Cespresso/CLumo/standalone/src/assets.rs

#![allow(dead_code)]

/// 8x8 LED matrix dot patterns.
/// Each `[u8; 8]` represents 8 rows, MSB=left pixel, LSB=right pixel.

// --- Faces ---

pub const FACE_SMILE: [u8; 8] = [0x00, 0x66, 0x66, 0x00, 0x00, 0x42, 0x3C, 0x00];
pub const FACE_BLINK: [u8; 8] = [0x00, 0x00, 0x66, 0x00, 0x00, 0x42, 0x3C, 0x00];
pub const FACE_SAD: [u8; 8] = [0x00, 0x66, 0x66, 0x00, 0x00, 0x3C, 0x42, 0x00];
pub const FACE_ANGRY: [u8; 8] = [0x00, 0x42, 0x66, 0x00, 0x00, 0x3C, 0x42, 0x00];
pub const FACE_HAPPY: [u8; 8] = [0x00, 0x66, 0x66, 0x00, 0x24, 0x42, 0x3C, 0x00];
pub const FACE_LOOK_LEFT: [u8; 8] = [0x00, 0xCC, 0xCC, 0x00, 0x00, 0x42, 0x3C, 0x00];
pub const FACE_LOOK_RIGHT: [u8; 8] = [0x00, 0x33, 0x33, 0x00, 0x00, 0x42, 0x3C, 0x00];

// --- Mode icons ---

pub const ICON_PET: [u8; 8] = FACE_SMILE;
/// An hourglass.
pub const ICON_POMODORO: [u8; 8] = [0x7E, 0x42, 0x24, 0x18, 0x18, 0x24, 0x42, 0x7E];
pub const ICON_DICE: [u8; 8] = DICE_5;

// --- Dice (1-6) ---

pub const DICE_1: [u8; 8] = [0x00, 0x00, 0x00, 0x18, 0x18, 0x00, 0x00, 0x00];
pub const DICE_2: [u8; 8] = [0x00, 0x60, 0x60, 0x00, 0x00, 0x06, 0x06, 0x00];
pub const DICE_3: [u8; 8] = [0x00, 0x60, 0x60, 0x18, 0x18, 0x06, 0x06, 0x00];
pub const DICE_4: [u8; 8] = [0x00, 0x66, 0x66, 0x00, 0x00, 0x66, 0x66, 0x00];
pub const DICE_5: [u8; 8] = [0x00, 0x66, 0x66, 0x18, 0x18, 0x66, 0x66, 0x00];
pub const DICE_6: [u8; 8] = [0x00, 0x66, 0x66, 0x66, 0x66, 0x66, 0x66, 0x00];

// --- Utility ---

pub const PATTERN_ALL_ON: [u8; 8] = [0xFF; 8];
pub const PATTERN_ALL_OFF: [u8; 8] = [0x00; 8];
