Cespresso/CLumo/companion/android/app/src/main/java/io/github/cespresso/clumo/ui/components/Components.kt

package io.github.cespresso.clumo.ui.components

import androidx.compose.animation.animateColor
import androidx.compose.animation.core.RepeatMode
import androidx.compose.animation.core.animateFloat
import androidx.compose.animation.core.infiniteRepeatable
import androidx.compose.animation.core.rememberInfiniteTransition
import androidx.compose.animation.core.tween
import androidx.compose.foundation.Canvas
import androidx.compose.foundation.background
import androidx.compose.foundation.border
import androidx.compose.foundation.clickable
import androidx.compose.foundation.interaction.MutableInteractionSource
import androidx.compose.foundation.layout.Arrangement
import androidx.compose.foundation.layout.Box
import androidx.compose.foundation.layout.Column
import androidx.compose.foundation.layout.ColumnScope
import androidx.compose.foundation.layout.Row
import androidx.compose.foundation.layout.fillMaxSize
import androidx.compose.foundation.layout.fillMaxWidth
import androidx.compose.foundation.layout.offset
import androidx.compose.foundation.layout.padding
import androidx.compose.foundation.layout.size
import androidx.compose.foundation.shape.CircleShape
import androidx.compose.foundation.shape.RoundedCornerShape
import androidx.compose.foundation.text.BasicTextField
import androidx.compose.material3.Slider
import androidx.compose.material3.SliderDefaults
import androidx.compose.material3.Text
import androidx.compose.runtime.Composable
import androidx.compose.runtime.getValue
import androidx.compose.runtime.mutableStateOf
import androidx.compose.runtime.remember
import androidx.compose.runtime.setValue
import androidx.compose.ui.Alignment
import androidx.compose.ui.Modifier
import androidx.compose.ui.draw.clip
import androidx.compose.ui.draw.drawBehind
import androidx.compose.ui.draw.shadow
import androidx.compose.ui.geometry.CornerRadius
import androidx.compose.ui.geometry.Offset
import androidx.compose.ui.geometry.Rect
import androidx.compose.ui.geometry.RoundRect
import androidx.compose.ui.graphics.Brush
import androidx.compose.ui.graphics.Color
import androidx.compose.ui.graphics.Path
import androidx.compose.ui.graphics.PathEffect
import androidx.compose.ui.graphics.PathOperation
import androidx.compose.ui.graphics.StrokeCap
import androidx.compose.ui.graphics.StrokeJoin
import androidx.compose.ui.graphics.drawscope.Stroke
import androidx.compose.ui.graphics.lerp
import androidx.compose.ui.res.stringResource
import androidx.compose.ui.semantics.Role
import androidx.compose.ui.semantics.contentDescription
import androidx.compose.ui.semantics.semantics
import androidx.compose.ui.text.TextStyle
import androidx.compose.ui.text.font.FontWeight
import androidx.compose.ui.text.style.TextAlign
import androidx.compose.ui.unit.Dp
import androidx.compose.ui.unit.dp
import androidx.compose.ui.unit.sp
import androidx.compose.ui.zIndex
import io.github.cespresso.clumo.R
import io.github.cespresso.clumo.design.ClumoColors
import io.github.cespresso.clumo.design.ContentTone
import io.github.cespresso.clumo.design.contentToneFor
import io.github.cespresso.clumo.domain.ConnectionState
import io.github.cespresso.clumo.domain.DeviceAppearance
import io.github.cespresso.clumo.ui.theme.LocalClumoAccents
import io.github.cespresso.clumo.ui.theme.RoundedFontFamily

// ---------------------------------------------------------------------------
// Connection-state visuals
// ---------------------------------------------------------------------------

@Composable
fun connectionLabel(state: ConnectionState): Pair<String, Color> =
    when (state) {
        ConnectionState.Ready -> stringResource(R.string.state_connected) to LocalClumoAccents.current.accent
        ConnectionState.Connecting,
        ConnectionState.Reconnecting,
        ConnectionState.Bonding,
        ConnectionState.Connected,
        ConnectionState.Synchronizing,
        -> stringResource(R.string.state_connecting) to ClumoColors.Muted
        ConnectionState.Error -> stringResource(R.string.state_error) to ClumoColors.Coral
        ConnectionState.Disconnected -> stringResource(R.string.state_disconnected) to ClumoColors.MutedLight
    }

// ---------------------------------------------------------------------------
// Brand motif: thick rounded L-corner stroke
// ---------------------------------------------------------------------------

@Composable
fun BrandCorner(
    size: Dp,
    stroke: Dp,
    modifier: Modifier = Modifier,
    color: Color = LocalClumoAccents.current.accent,
) {
    Canvas(modifier = modifier.size(size)) {
        val sw = stroke.toPx()
        val half = sw / 2f
        val side = this.size.width
        // Match the launcher foreground: a quarter-size inner curve with rounded ends.
        // Keeping endpoints half a stroke inside the bounds prevents the round caps from
        // extending beyond this composable's requested size.
        val centerRadius = (side / 4f).coerceAtLeast(1f)
        val terminal = (side - half).coerceAtLeast(half)
        val path = Path().apply {
            moveTo(half, terminal)
            lineTo(half, half + centerRadius)
            arcTo(
                rect = Rect(half, half, half + centerRadius * 2, half + centerRadius * 2),
                startAngleDegrees = 180f,
                sweepAngleDegrees = 90f,
                forceMoveTo = false,
            )
            lineTo(terminal, half)
        }
        drawPath(
            path,
            color,
            style = Stroke(width = sw, cap = StrokeCap.Round, join = StrokeJoin.Round),
        )
    }
}

// ---------------------------------------------------------------------------
// Pill buttons
// ---------------------------------------------------------------------------

@Composable
fun CtaPillButton(
    text: String,
    onClick: () -> Unit,
    modifier: Modifier = Modifier,
    fontSize: androidx.compose.ui.unit.TextUnit = 16.sp,
    verticalPadding: Dp = 16.dp,
    enabled: Boolean = true,
) {
    val accents = LocalClumoAccents.current
    Box(
        modifier = modifier
            .shadow(8.dp, RoundedCornerShape(999.dp), ambientColor = accents.cta, spotColor = accents.cta)
            .clip(RoundedCornerShape(999.dp))
            .background(accents.cta)
            .clickable(enabled = enabled, onClick = onClick)
            .padding(horizontal = 24.dp, vertical = verticalPadding),
        contentAlignment = Alignment.Center,
    ) {
        Text(
            text = text,
            color = accents.onCta,
            fontSize = fontSize,
            fontWeight = FontWeight.Bold,
            fontFamily = RoundedFontFamily,
        )
    }
}

@Composable
fun OutlinePillButton(
    text: String,
    onClick: () -> Unit,
    modifier: Modifier = Modifier,
    fontSize: androidx.compose.ui.unit.TextUnit = 15.sp,
    verticalPadding: Dp = 14.dp,
    textColor: Color = ClumoColors.Text,
    enabled: Boolean = true,
) {
    Box(
        modifier = modifier
            .clip(RoundedCornerShape(999.dp))
            .background(ClumoColors.White)
            .border(1.5.dp, ClumoColors.OutlineBorder, RoundedCornerShape(999.dp))
            .clickable(enabled = enabled, onClick = onClick)
            .padding(horizontal = 16.dp, vertical = verticalPadding),
        contentAlignment = Alignment.Center,
    ) {
        Text(
            text = text,
            color = textColor,
            fontSize = fontSize,
            fontWeight = FontWeight.Bold,
            fontFamily = RoundedFontFamily,
        )
    }
}

// ---------------------------------------------------------------------------
// Help affordance: circular "?" that opens an explanatory dialog
// ---------------------------------------------------------------------------

/**
 * The tap target is a full 48.dp even though the ring is 30.dp, so the badge
 * stays reachable when it sits beside a heading.
 */
@Composable
fun HelpBadge(
    description: String,
    onClick: () -> Unit,
    modifier: Modifier = Modifier,
) {
    val accent = LocalClumoAccents.current.accent
    Box(
        modifier = modifier
            .size(48.dp)
            .clip(CircleShape)
            .semantics { contentDescription = description }
            .clickable(role = Role.Button, onClickLabel = description, onClick = onClick),
        contentAlignment = Alignment.Center,
    ) {
        Box(
            modifier = Modifier
                .size(30.dp)
                .clip(CircleShape)
                .background(ClumoColors.White)
                .border(1.5.dp, accent, CircleShape),
            contentAlignment = Alignment.Center,
        ) {
            Text(
                text = "?",
                fontSize = 15.sp,
                fontWeight = FontWeight.ExtraBold,
                fontFamily = RoundedFontFamily,
                color = accent,
            )
        }
    }
}

// ---------------------------------------------------------------------------
// CLumo device: two independently colored physical knobs on top of the face.
// Each knob is a two-tier bump: a wider boss with the cap above it, both in the
// cap's color like the real hardware.
// ---------------------------------------------------------------------------

@Composable
fun ClumoDevice(
    bits: Long,
    size: Dp,
    modifier: Modifier = Modifier,
    appearance: DeviceAppearance = DeviceAppearance.DEFAULT,
    connectionState: ConnectionState? = null,
    litAlpha: Float = 1f,
    glow: Boolean = true,
    shadowElevation: Dp = 0.dp,
) {
    Box(modifier = modifier) {
        ConnectionRingCanvas(
            state = connectionState,
            size = size + 8.dp,
            modifier = Modifier
                .align(Alignment.BottomCenter)
                .offset(y = (-4).dp)
                .zIndex(DeviceVisualLayer.ConnectionRing.zIndex),
        )
        Column(
            modifier = Modifier.zIndex(DeviceVisualLayer.PhysicalDevice.zIndex),
            horizontalAlignment = Alignment.CenterHorizontally,
        ) {
            DeviceKnobs(faceSize = size, appearance = appearance)
            Box(
                modifier = Modifier
                    .size(size + 8.dp)
                    .offset(y = (-4).dp),
                contentAlignment = Alignment.Center,
            ) {
                DeviceFace(
                    bits = bits,
                    frameColor = appearance.enclosureColor.toComposeColor(),
                    ledColor = appearance.ledColor.toComposeColor(),
                    size = size,
                    frameOutline = if (
                        contentToneFor(appearance.enclosureColor) == ContentTone.Dark
                    ) {
                        ClumoColors.OutlineBorder
                    } else {
                        null
                    },
                    litAlpha = litAlpha,
                    glow = glow,
                    shadowElevation = shadowElevation,
                )
            }
        }
    }
}

@Composable
private fun ConnectionRingCanvas(
    state: ConnectionState?,
    size: Dp,
    modifier: Modifier = Modifier,
) {
    val ring = state?.let(::connectionRingFor) ?: ConnectionRing.None
    if (ring == ConnectionRing.None) return
    val ringColor = if (ring == ConnectionRing.Pulse) {
        val transition = rememberInfiniteTransition(label = "connectionRingPulse")
        val color by transition.animateColor(
            initialValue = ClumoColors.Gray,
            targetValue = LocalClumoAccents.current.accent,
            animationSpec = infiniteRepeatable(tween(700), RepeatMode.Reverse),
            label = "connectionRingColor",
        )
        color
    } else {
        ClumoColors.Coral
    }
    Canvas(modifier = modifier.size(size)) {
        drawRoundRect(
            color = ringColor,
            cornerRadius = CornerRadius(size.toPx() * 42f / 188f),
            style = Stroke(width = 3.dp.toPx()),
        )
    }
}

// Knob ratios are fractions of a 168dp frame while DeviceFace's corner and
// padding defaults are fractions of 188dp. Both scale off the same face size,
// so they compose correctly; don't "unify" the denominators.
@Composable
private fun DeviceKnobs(faceSize: Dp, appearance: DeviceAppearance) {
    Row(
        horizontalArrangement = Arrangement.spacedBy(faceSize * 16f / 168f),
        // Tuck 1dp under the face so no hairline gap opens between them. The face
        // is the later sibling, so it paints over the overlap.
        modifier = Modifier.offset(y = 1.dp),
    ) {
        DeviceKnob(
            faceSize = faceSize,
            color = appearance.buttonAColor.toComposeColor(),
            outline = if (contentToneFor(appearance.buttonAColor) == ContentTone.Dark) {
                ClumoColors.OutlineBorder
            } else {
                null
            },
        )
        DeviceKnob(
            faceSize = faceSize,
            color = appearance.buttonBColor.toComposeColor(),
            outline = if (contentToneFor(appearance.buttonBColor) == ContentTone.Dark) {
                ClumoColors.OutlineBorder
            } else {
                null
            },
        )
    }
}

/**
 * One knob as a single 凸 path so the cap and boss share one outline. The tier
 * step comes from the silhouette and a shading gradient because Compose draws
 * siblings in declaration order regardless of elevation, so a shadow the cap
 * casts would be painted over by the boss.
 */
@Composable
private fun DeviceKnob(faceSize: Dp, color: Color, outline: Color? = null) {
    val capWidth = faceSize * 18f / 168f
    val capHeight = faceSize * 10f / 168f
    val bossWidth = faceSize * 28f / 168f
    val bossHeight = faceSize * 8f / 168f
    val capCorner = faceSize * 6f / 168f
    val bossCorner = faceSize * 5f / 168f
    Canvas(modifier = Modifier.size(width = bossWidth, height = capHeight + bossHeight)) {
        // Held back from the sides and top so the outline stays inside the canvas.
        // Applied even when this knob has no outline, so both are the same height.
        val inset = 0.5.dp.toPx()
        val capBottom = capHeight.toPx()
        val capLeft = (size.width - capWidth.toPx()) / 2f
        val cap = Path().apply {
            addRoundRect(
                RoundRect(
                    // Overlap the boss by a pixel so the union leaves no seam.
                    rect = Rect(capLeft, inset, capLeft + capWidth.toPx(), capBottom + 1f),
                    topLeft = CornerRadius(capCorner.toPx()),
                    topRight = CornerRadius(capCorner.toPx()),
                    bottomRight = CornerRadius.Zero,
                    bottomLeft = CornerRadius.Zero,
                ),
            )
        }
        val boss = Path().apply {
            addRoundRect(
                RoundRect(
                    rect = Rect(inset, capBottom, size.width - inset, size.height),
                    topLeft = CornerRadius(bossCorner.toPx()),
                    topRight = CornerRadius(bossCorner.toPx()),
                    bottomRight = CornerRadius.Zero,
                    bottomLeft = CornerRadius.Zero,
                ),
            )
        }
        val knob = Path().apply { op(cap, boss, PathOperation.Union) }
        // Light on each tier's top edge, shade at its base: the crease at the
        // junction is what makes the two tiers read as a step.
        val junction = capBottom / size.height
        drawPath(
            path = knob,
            brush = Brush.verticalGradient(
                0f to lerp(color, Color.White, 0.10f),
                junction * 0.97f to lerp(color, Color.Black, 0.07f),
                junction to lerp(color, Color.White, 0.14f),
                1f to lerp(color, Color.Black, 0.09f),
            ),
        )
        if (outline != null) {
            drawPath(path = knob, color = outline, style = Stroke(width = 1.dp.toPx()))
        }
    }
}

// ---------------------------------------------------------------------------
// Device face: colored frame + inner panel + 8x8 round dots
// ---------------------------------------------------------------------------

@Composable
fun DeviceFace(
    bits: Long,
    frameColor: Color,
    size: Dp,
    modifier: Modifier = Modifier,
    ledColor: Color = LocalClumoAccents.current.led,
    frameOutline: Color? = null,
    frameCorner: Dp = size * 42f / 188f,
    framePadding: Dp = size * 23f / 188f,
    innerCorner: Dp = size * 21f / 188f,
    gridPadding: Dp = size * 13f / 188f,
    litAlpha: Float = 1f,
    glow: Boolean = true,
    shadowElevation: Dp = 0.dp,
) {
    Box(
        modifier = modifier
            .then(
                if (shadowElevation > 0.dp) {
                    Modifier.shadow(shadowElevation, RoundedCornerShape(frameCorner))
                } else {
                    Modifier
                },
            )
            .size(size)
            .clip(RoundedCornerShape(frameCorner))
            .background(frameColor)
            .then(
                if (frameOutline != null) {
                    Modifier.border(1.dp, frameOutline, RoundedCornerShape(frameCorner))
                } else {
                    Modifier
                },
            )
            .padding(framePadding),
    ) {
        Box(
            modifier = Modifier
                .fillMaxSize()
                .clip(RoundedCornerShape(innerCorner))
                .background(ClumoColors.Panel)
                .padding(gridPadding),
        ) {
            DotGrid(bits = bits, ledColor = ledColor, litAlpha = litAlpha, glow = glow)
        }
    }
}

@Composable
fun DotGrid(
    bits: Long,
    modifier: Modifier = Modifier,
    ledColor: Color = LocalClumoAccents.current.led,
    litAlpha: Float = 1f,
    glow: Boolean = true,
) {
    Canvas(modifier = modifier.fillMaxSize()) {
        val cellW = this.size.width / 8f
        val cellH = this.size.height / 8f
        val dotRadius = minOf(cellW, cellH) * 0.38f
        for (row in 0 until 8) {
            for (col in 0 until 8) {
                val on = (bits shr (row * 8 + col)) and 1L == 1L
                val center = Offset(cellW * (col + 0.5f), cellH * (row + 0.5f))
                if (on) {
                    if (glow) {
                        drawCircle(
                            brush = Brush.radialGradient(
                                colors = listOf(
                                    ledColor.copy(alpha = 0.55f * litAlpha),
                                    ledColor.copy(alpha = 0f),
                                ),
                                center = center,
                                radius = dotRadius * 2.1f,
                            ),
                            radius = dotRadius * 2.1f,
                            center = center,
                        )
                    }
                    drawCircle(
                        color = ledColor.copy(alpha = litAlpha),
                        radius = dotRadius,
                        center = center,
                    )
                } else {
                    drawCircle(
                        color = ClumoColors.OffDot,
                        radius = dotRadius,
                        center = center,
                    )
                }
            }
        }
    }
}

// ---------------------------------------------------------------------------
// Segmented control (2x2 grid with white active thumb)
// ---------------------------------------------------------------------------

@Composable
fun SegmentedControl(
    items: List<String>,
    selectedIndex: Int,
    onSelect: (Int) -> Unit,
    modifier: Modifier = Modifier,
) {
    Column(
        modifier = modifier
            .clip(RoundedCornerShape(22.dp))
            .background(ClumoColors.SegBackground)
            .padding(5.dp),
        verticalArrangement = Arrangement.spacedBy(4.dp),
    ) {
        items.chunked(2).forEachIndexed { rowIndex, rowItems ->
            Row(
                modifier = Modifier.fillMaxWidth(),
                horizontalArrangement = Arrangement.spacedBy(4.dp),
            ) {
                rowItems.forEachIndexed { columnIndex, label ->
                    val index = rowIndex * 2 + columnIndex
                    val active = index == selectedIndex
                    Box(
                        modifier = Modifier
                            .weight(1f)
                            .then(
                                if (active) {
                                    Modifier.shadow(3.dp, RoundedCornerShape(999.dp))
                                } else {
                                    Modifier
                                },
                            )
                            .clip(RoundedCornerShape(999.dp))
                            .background(if (active) LocalClumoAccents.current.knob else Color.Transparent)
                            .clickable(
                                interactionSource = remember { MutableInteractionSource() },
                                indication = null,
                            ) { onSelect(index) }
                            .padding(vertical = 9.dp, horizontal = 6.dp),
                        contentAlignment = Alignment.Center,
                    ) {
                        Text(
                            text = label,
                            fontSize = 13.sp,
                            fontWeight = FontWeight.ExtraBold,
                            fontFamily = RoundedFontFamily,
                            color = if (active) ClumoColors.Text else ClumoColors.SegInactiveText,
                            maxLines = 1,
                        )
                    }
                }
            }
        }
    }
}

// ---------------------------------------------------------------------------
// Scanning dots animation
// ---------------------------------------------------------------------------

@Composable
fun ScanningIndicator(modifier: Modifier = Modifier) {
    Row(
        modifier = modifier.padding(16.dp),
        horizontalArrangement = Arrangement.spacedBy(10.dp, Alignment.CenterHorizontally),
        verticalAlignment = Alignment.CenterVertically,
    ) {
        val transition = rememberInfiniteTransition(label = "scanDots")
        for (i in 0 until 3) {
            val alpha by transition.animateFloat(
                initialValue = 0.2f,
                targetValue = 1f,
                animationSpec = infiniteRepeatable(
                    animation = tween(600, delayMillis = i * 200),
                    repeatMode = RepeatMode.Reverse,
                ),
                label = "scanDot$i",
            )
            Box(
                modifier = Modifier
                    .size(10.dp)
                    .clip(CircleShape)
                    .background(LocalClumoAccents.current.accent.copy(alpha = alpha)),
            )
        }
        Text(
            text = stringResource(R.string.list_scanning),
            fontSize = 14.sp,
            fontWeight = FontWeight.Bold,
            fontFamily = RoundedFontFamily,
            color = ClumoColors.Muted,
            modifier = Modifier.padding(start = 4.dp),
        )
    }
}

// ---------------------------------------------------------------------------
// Sliders
// ---------------------------------------------------------------------------

@Composable
fun ClumoSlider(
    value: Float,
    onValueChange: (Float) -> Unit,
    modifier: Modifier = Modifier,
    enabled: Boolean = true,
    onValueChangeFinished: () -> Unit = {},
) {
    Slider(
        value = value,
        onValueChange = onValueChange,
        onValueChangeFinished = onValueChangeFinished,
        valueRange = 0f..100f,
        enabled = enabled,
        modifier = modifier,
        colors = SliderDefaults.colors(
            thumbColor = LocalClumoAccents.current.accent,
            activeTrackColor = LocalClumoAccents.current.accent,
            inactiveTrackColor = ClumoColors.ChipBorder,
        ),
    )
}

@Composable
fun ClumoToggleSwitch(
    checked: Boolean,
    onCheckedChange: (Boolean) -> Unit,
    modifier: Modifier = Modifier,
) {
    val accents = LocalClumoAccents.current
    Box(
        modifier = modifier
            .size(width = 48.dp, height = 28.dp)
            .clip(RoundedCornerShape(999.dp))
            .background(if (checked) accents.accent else ClumoColors.SwitchOff)
            .clickable { onCheckedChange(!checked) }
            .padding(3.dp),
        contentAlignment = if (checked) Alignment.CenterEnd else Alignment.CenterStart,
    ) {
        Box(
            modifier = Modifier
                .size(22.dp)
                .shadow(2.dp, CircleShape)
                .clip(CircleShape)
                .background(accents.knob),
        )
    }
}

// ---------------------------------------------------------------------------
// Text input + name dialogs (rename device / save pattern)
// ---------------------------------------------------------------------------

@Composable
fun ClumoTextField(
    value: String,
    onValueChange: (String) -> Unit,
    modifier: Modifier = Modifier,
    placeholder: String? = null,
) {
    BasicTextField(
        value = value,
        onValueChange = onValueChange,
        singleLine = true,
        textStyle = TextStyle(
            fontFamily = RoundedFontFamily,
            fontSize = 15.sp,
            fontWeight = FontWeight.Bold,
            color = ClumoColors.Text,
        ),
        modifier = modifier,
        decorationBox = { innerTextField ->
            Box(
                modifier = Modifier
                    .clip(RoundedCornerShape(16.dp))
                    .background(ClumoColors.Background)
                    .border(1.5.dp, ClumoColors.OutlineBorder, RoundedCornerShape(16.dp))
                    .padding(horizontal = 16.dp, vertical = 13.dp),
            ) {
                if (value.isEmpty() && placeholder != null) {
                    Text(
                        text = placeholder,
                        fontFamily = RoundedFontFamily,
                        fontSize = 15.sp,
                        fontWeight = FontWeight.Bold,
                        color = ClumoColors.MutedLight,
                    )
                }
                innerTextField()
            }
        },
    )
}

@Composable
fun NameInputDialog(
    title: String,
    initialValue: String,
    placeholder: String?,
    onConfirm: (String) -> Unit,
    onDismiss: () -> Unit,
    modifier: Modifier = Modifier,
) {
    var text by remember { mutableStateOf(initialValue) }
    DialogCard(onDismiss = onDismiss, modifier = modifier) {
        DialogTitle(title)
        ClumoTextField(
            value = text,
            onValueChange = { text = it },
            placeholder = placeholder,
            modifier = Modifier.fillMaxWidth(),
        )
        Row(horizontalArrangement = Arrangement.spacedBy(10.dp)) {
            OutlinePillButton(
                text = stringResource(R.string.dialog_cancel),
                onClick = onDismiss,
                fontSize = 14.sp,
                verticalPadding = 12.dp,
                modifier = Modifier.weight(1f),
            )
            CtaPillButton(
                text = stringResource(R.string.dialog_save),
                onClick = { onConfirm(text) },
                fontSize = 14.sp,
                verticalPadding = 12.dp,
                modifier = Modifier.weight(1f),
            )
        }
    }
}

/** CLumo-styled two-action dialog used for blocking, user-actionable problems. */
@Composable
fun ClumoActionDialog(
    title: String,
    body: String,
    confirmText: String,
    onConfirm: () -> Unit,
    onDismiss: () -> Unit,
    modifier: Modifier = Modifier,
    dismissText: String = stringResource(R.string.dialog_cancel),
) {
    DialogCard(onDismiss = onDismiss, modifier = modifier) {
        DialogTitle(title)
        DialogBody(body)
        Row(horizontalArrangement = Arrangement.spacedBy(10.dp)) {
            OutlinePillButton(
                text = dismissText,
                onClick = onDismiss,
                fontSize = 14.sp,
                verticalPadding = 12.dp,
                modifier = Modifier.weight(1f),
            )
            CtaPillButton(
                text = confirmText,
                onClick = onConfirm,
                fontSize = 14.sp,
                verticalPadding = 12.dp,
                modifier = Modifier.weight(1f),
            )
        }
    }
}

/** CLumo-styled single-action dialog for explaining a feature. */
@Composable
fun ClumoInfoDialog(
    title: String,
    body: String,
    onDismiss: () -> Unit,
    modifier: Modifier = Modifier,
    acknowledgeText: String = stringResource(R.string.dialog_acknowledge),
) {
    DialogCard(onDismiss = onDismiss, modifier = modifier) {
        DialogTitle(title)
        DialogBody(body)
        CtaPillButton(
            text = acknowledgeText,
            onClick = onDismiss,
            fontSize = 14.sp,
            verticalPadding = 12.dp,
            modifier = Modifier.fillMaxWidth(),
        )
    }
}

/** Squircle white card shared by every CLumo dialog. */
@Composable
private fun DialogCard(
    onDismiss: () -> Unit,
    modifier: Modifier = Modifier,
    content: @Composable ColumnScope.() -> Unit,
) {
    androidx.compose.ui.window.Dialog(onDismissRequest = onDismiss) {
        Column(
            modifier = modifier
                .fillMaxWidth()
                .clip(RoundedCornerShape(26.dp))
                .background(ClumoColors.White)
                .padding(22.dp),
            verticalArrangement = Arrangement.spacedBy(16.dp),
            content = content,
        )
    }
}

@Composable
private fun DialogTitle(text: String) {
    Text(
        text = text,
        fontSize = 16.sp,
        fontWeight = FontWeight.ExtraBold,
        fontFamily = RoundedFontFamily,
        color = ClumoColors.Text,
    )
}

@Composable
private fun DialogBody(text: String) {
    Text(
        text = text,
        fontSize = 13.5.sp,
        fontWeight = FontWeight.Medium,
        fontFamily = RoundedFontFamily,
        color = ClumoColors.Muted,
        lineHeight = 21.sp,
    )
}

// ---------------------------------------------------------------------------
// Dashed rounded border (empty states / "add new" tile)
// ---------------------------------------------------------------------------

fun Modifier.dashedBorder(
    color: Color,
    strokeWidth: Dp,
    cornerRadius: Dp,
    dashLength: Dp = 8.dp,
    gapLength: Dp = 7.dp,
): Modifier =
    drawBehind {
        val stroke = Stroke(
            width = strokeWidth.toPx(),
            pathEffect = PathEffect.dashPathEffect(
                floatArrayOf(dashLength.toPx(), gapLength.toPx()),
                0f,
            ),
        )
        drawRoundRect(
            color = color,
            style = stroke,
            cornerRadius = CornerRadius(cornerRadius.toPx()),
        )
    }
