Cespresso/CLumo/companion/firmware/src/utils/button.rs

use esp_idf_hal::gpio::{AnyIOPin, Input, PinDriver, Pull};
use esp_idf_hal::sys::EspError;
use std::time::Instant;

pub struct Button<'d> {
    pin: PinDriver<'d, AnyIOPin, Input>,
    last_state: bool,
    press_start: Option<Instant>,
    debounce_ms: u32,
}

impl<'d> Button<'d> {
    pub fn new(pin: AnyIOPin, debounce_ms: u32) -> Result<Self, EspError> {
        let mut pin_driver = PinDriver::input(pin)?;
        pin_driver.set_pull(Pull::Up)?;

        Ok(Self {
            pin: pin_driver,
            last_state: true, // Pull-up: HIGH when not pressed
            press_start: None,
            debounce_ms,
        })
    }

    /// Returns true once per press, on release.
    pub fn poll(&mut self) -> bool {
        let current = self.pin.is_high();
        let previous = std::mem::replace(&mut self.last_state, current);

        // Press start (HIGH -> LOW)
        if previous && !current {
            self.press_start = Some(Instant::now());
            return false;
        }

        // Press end (LOW -> HIGH)
        if !previous && current {
            if let Some(start) = self.press_start.take() {
                return start.elapsed().as_millis() >= self.debounce_ms as u128;
            }
        }

        false
    }
}

pub struct Buttons<'d> {
    pub red: Button<'d>,
    pub white: Button<'d>,
}

impl<'d> Buttons<'d> {
    /// The debounce threshold assumes the main loop's poll cadence; shortening the
    /// loop period would make it start rejecting real presses.
    pub fn new(red_pin: AnyIOPin, white_pin: AnyIOPin) -> Result<Self, EspError> {
        Ok(Self {
            red: Button::new(red_pin, 50)?,
            white: Button::new(white_pin, 50)?,
        })
    }
}
